mingo-git/Smartender/CAD-Files/01_stepper_motor/01_stepper_motor_body.stl

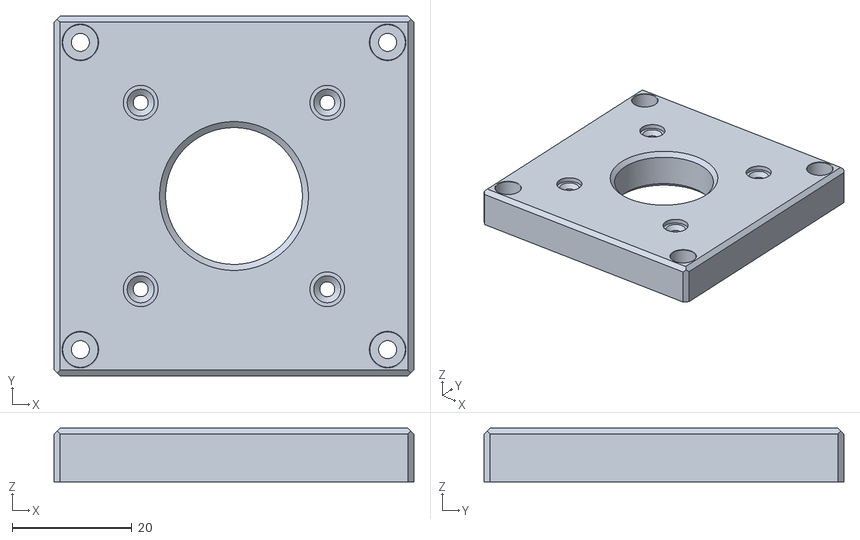
[picture p22: CAD file, 2024-11-23]
CAD-Files/01_stepper_motor/01_stepper_motor_body.stl
60.0 x 60.0 x 9.00
