mingo-git/Smartender/CAD-Files/02_gantry_rails/01_ganrtry_back_bell_grip.stl

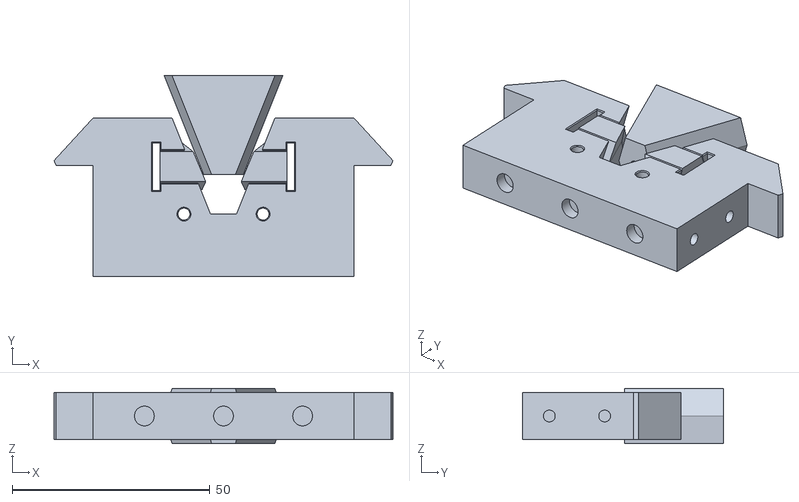
[picture p23: CAD file, 2025-01-10]
CAD-Files/02_gantry_rails/01_ganrtry_back_bell_grip.stl
85.7 x 50.7 x 14.0
