mingo-git/Smartender/CAD-Files/06_linar_servo/01_liear_servo_adapter_02.stl

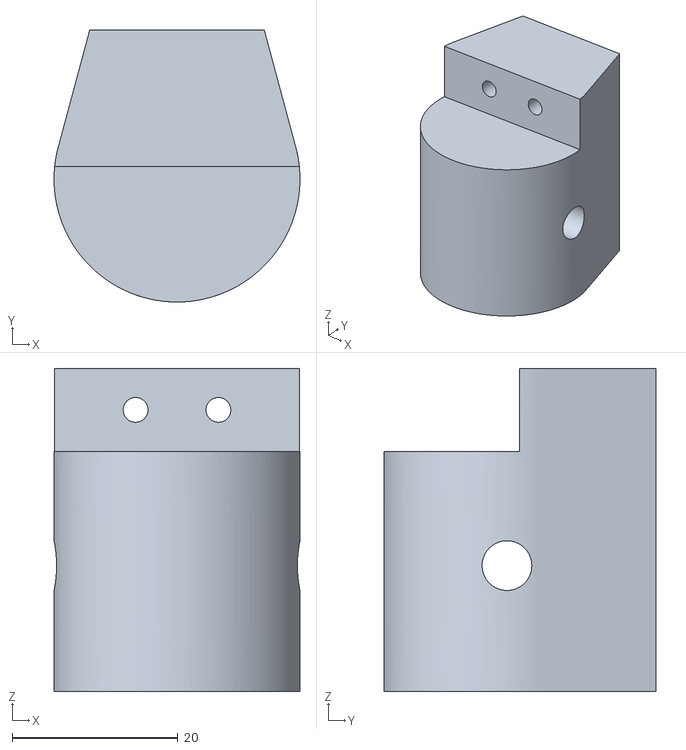
[picture p24: CAD file, 2025-01-10]
CAD-Files/06_linar_servo/01_liear_servo_adapter_02.stl
29.7 x 32.9 x 39.0
