mingo-git/Smartender/CAD-Files/06_linar_servo/01_liear_servo_adapter_06.stl

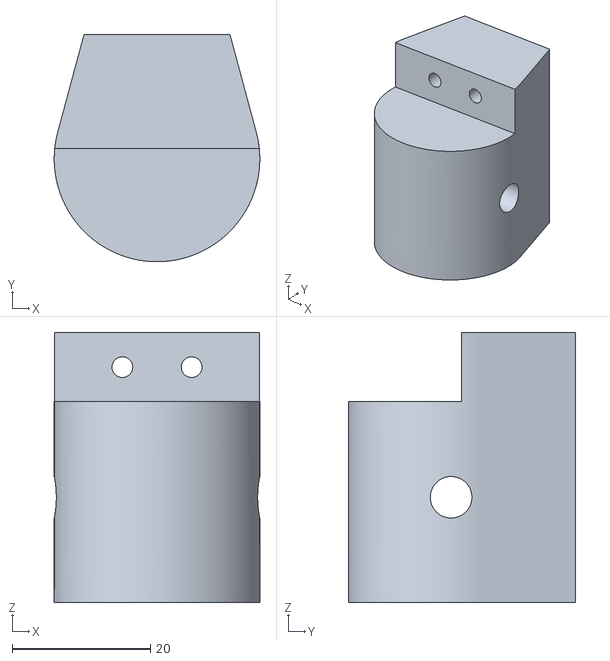
[picture p25: CAD file, 2025-01-10]
CAD-Files/06_linar_servo/01_liear_servo_adapter_06.stl
29.7 x 32.9 x 39.0
